HackershubNL/SmokeyMcSmokerson/Hardware/Smoker/Fan Mount Front.SLDPRT

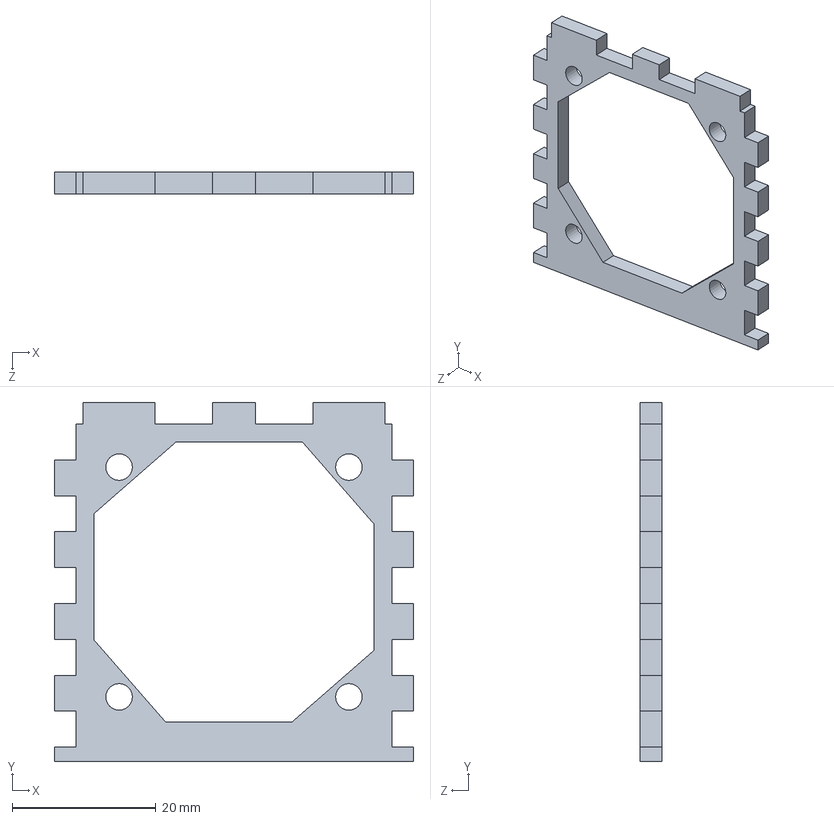
[picture p20: CAD file, 2019-05-26]
Hardware/Smoker/Fan Mount Front.SLDPRT
50.0 x 50.0 x 3.00 mm
