HackershubNL/SmokeyMcSmokerson/Hardware/Smoker/Inlet Spreader.SLDPRT

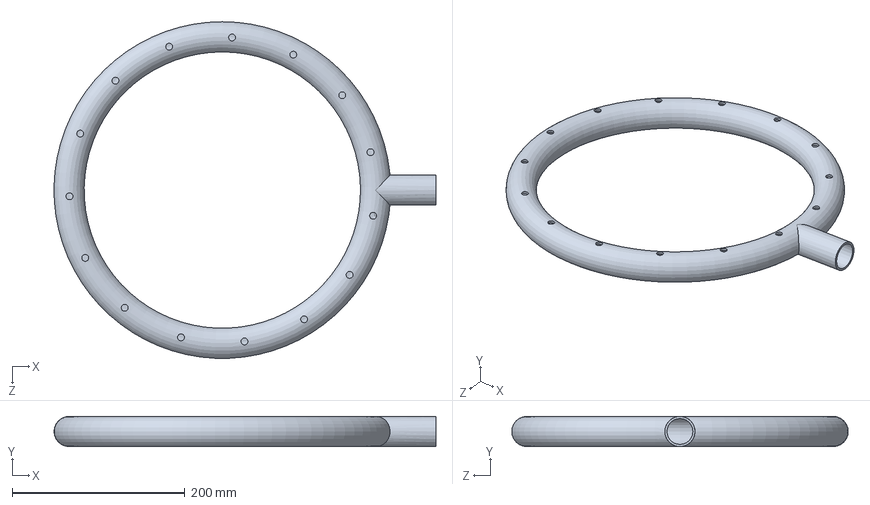
[picture p21: CAD file, 2019-05-26]
Hardware/Smoker/Inlet Spreader.SLDPRT
442.5 x 35.0 x 389.8 mm
