HackershubNL/SmokeyMcSmokerson/Hardware/Smoker/Controller Bracket V2.SLDPRT

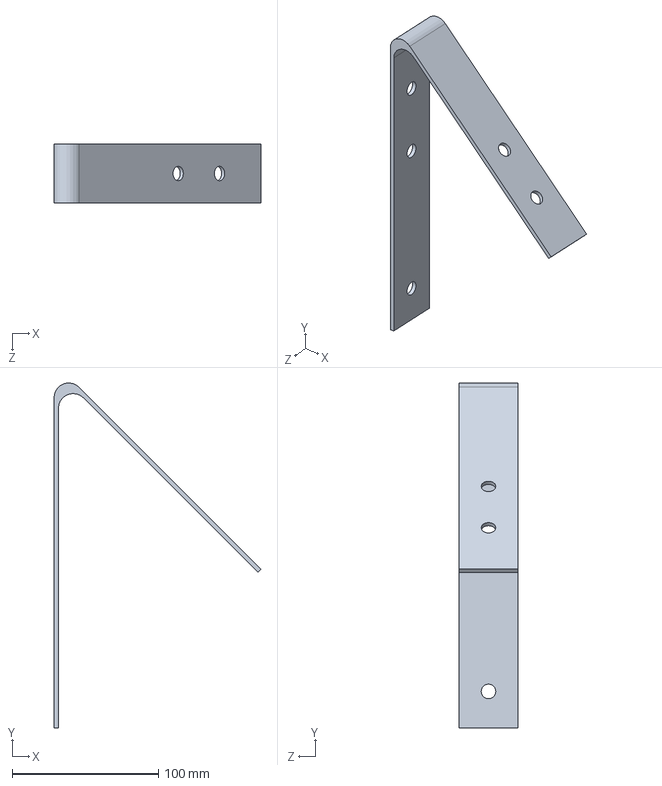
[picture p22: CAD file, 2019-05-26]
Hardware/Smoker/Controller Bracket V2.SLDPRT
141.4 x 235.8 x 40.0 mm
