HackershubNL/SmokeyMcSmokerson/Hardware/Smoker/Barrel.SLDPRT

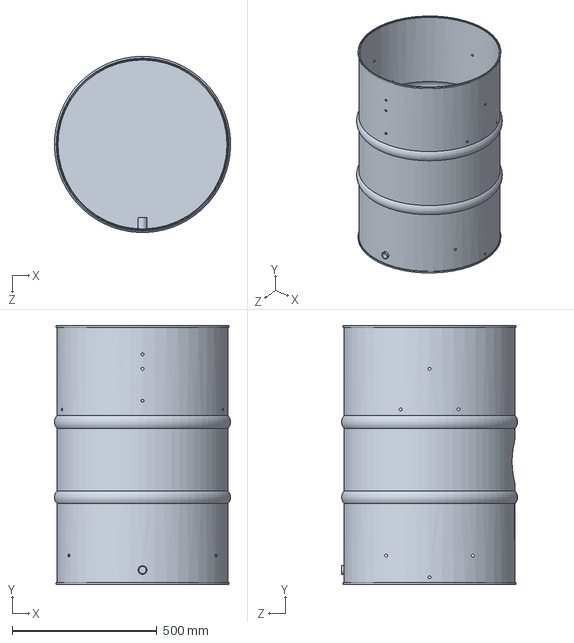
[picture p23: CAD file, 2019-05-26]
Hardware/Smoker/Barrel.SLDPRT
608.8 x 895.1 x 609.3 mm
