HackershubNL/SmokeyMcSmokerson/Hardware/Smoker/Header 2_54 Vertical 1x4.SLDPRT

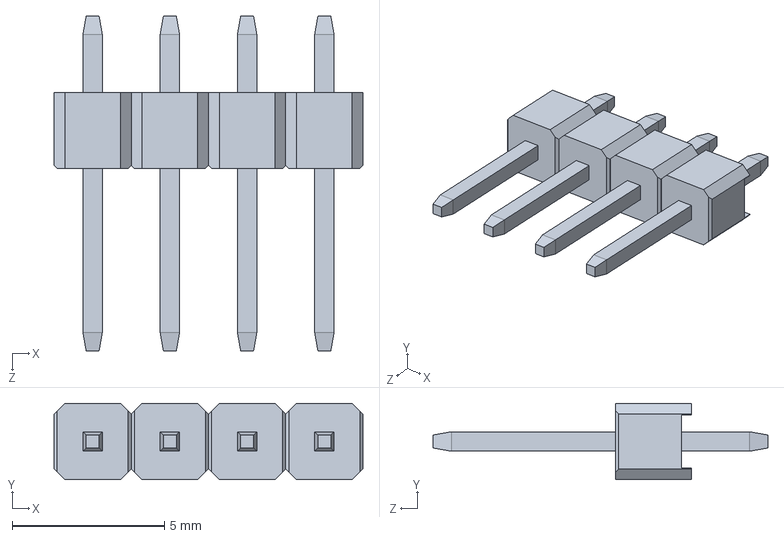
[picture p24: CAD file, 2019-05-26]
Hardware/Smoker/Header 2_54 Vertical 1x4.SLDPRT
10.2 x 2.50 x 11.0 mm
