HackershubNL/SmokeyMcSmokerson/Hardware/Smoker/Grill.SLDPRT

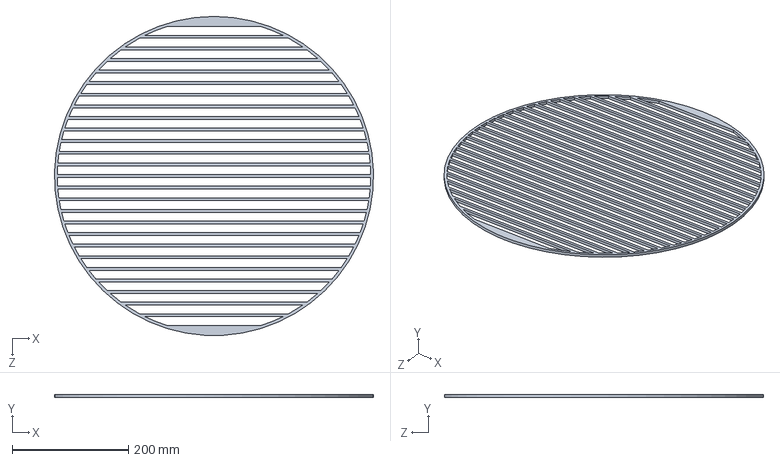
[picture p25: CAD file, 2019-05-26]
Hardware/Smoker/Grill.SLDPRT
549.8 x 5.00 x 550.0 mm
