HackershubNL/SmokeyMcSmokerson/Hardware/Smoker/Fan Mount Base.SLDPRT

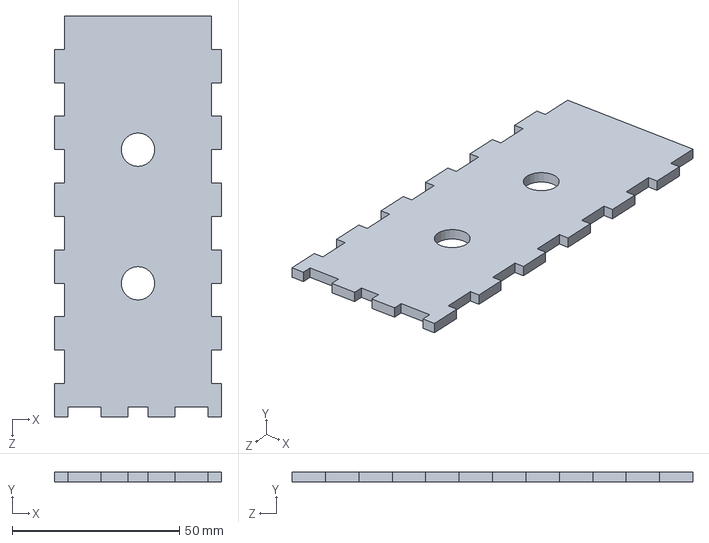
[picture p26: CAD file, 2019-05-26]
Hardware/Smoker/Fan Mount Base.SLDPRT
50.0 x 3.00 x 120.0 mm
