HackershubNL/SmokeyMcSmokerson/Hardware/Smoker/Led.SLDPRT

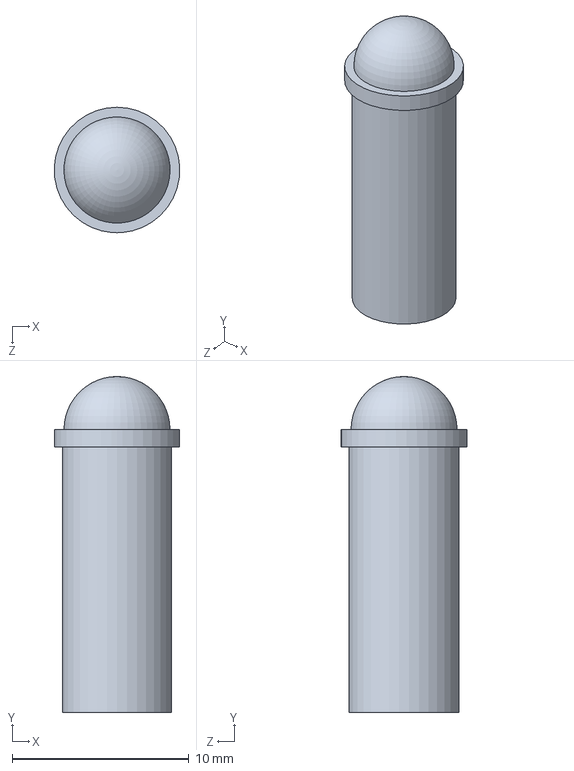
[picture p27: CAD file, 2019-05-26]
Hardware/Smoker/Led.SLDPRT
7.09 x 19.0 x 7.10 mm
