HackershubNL/SmokeyMcSmokerson/Hardware/Smoker/Controller Bracket.SLDPRT

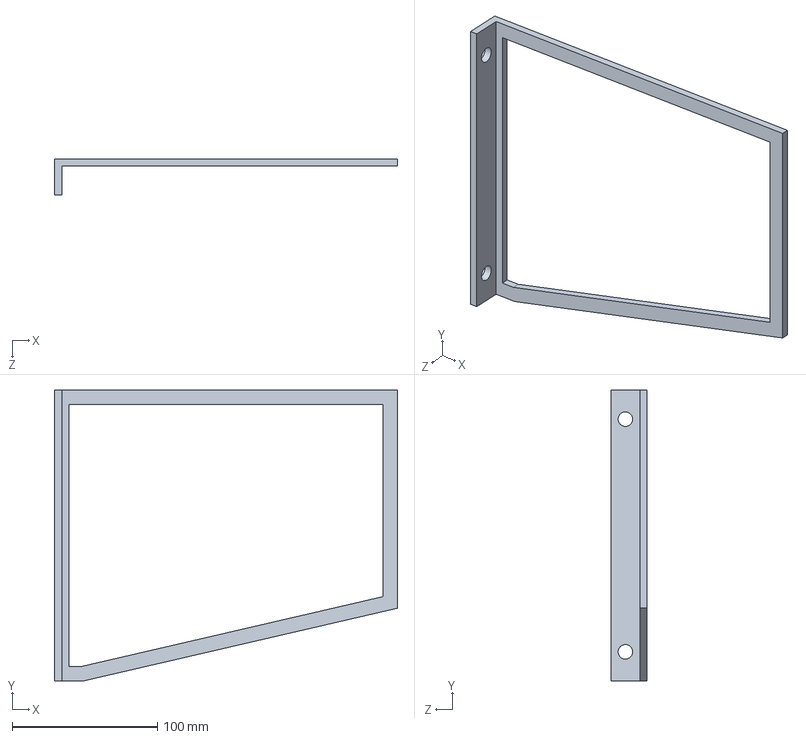
[picture p28: CAD file, 2019-05-26]
Hardware/Smoker/Controller Bracket.SLDPRT
235.9 x 200.0 x 25.0 mm
