HackershubNL/SmokeyMcSmokerson/Hardware/Smoker/Controller Box Base.SLDPRT

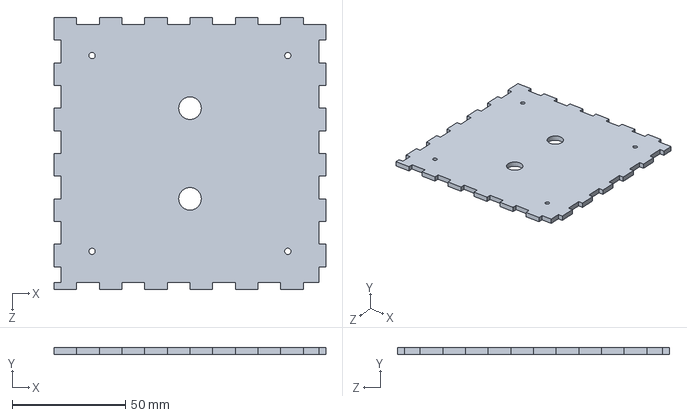
[picture p29: CAD file, 2019-05-26]
Hardware/Smoker/Controller Box Base.SLDPRT
120.0 x 3.00 x 120.0 mm
