HackershubNL/SmokeyMcSmokerson/Hardware/Smoker/GPIO Header.SLDPRT

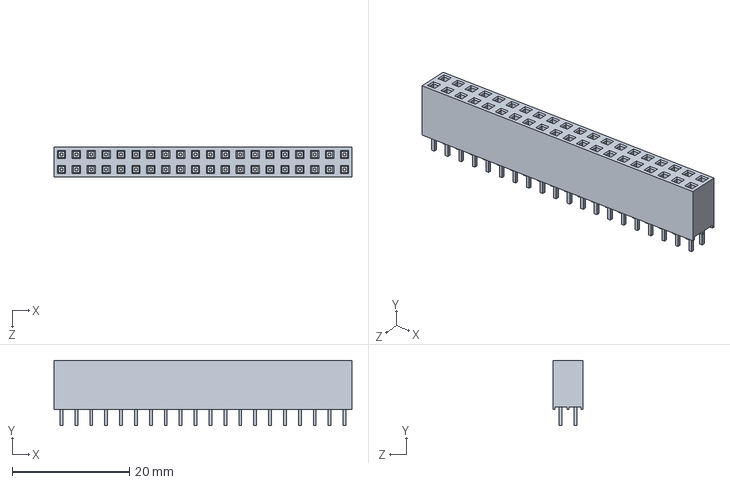
[picture p30: CAD file, 2019-05-26]
Hardware/Smoker/GPIO Header.SLDPRT
50.8 x 11.1 x 5.08 mm
