HackershubNL/SmokeyMcSmokerson/Hardware/Smoker/Water Pan.SLDPRT

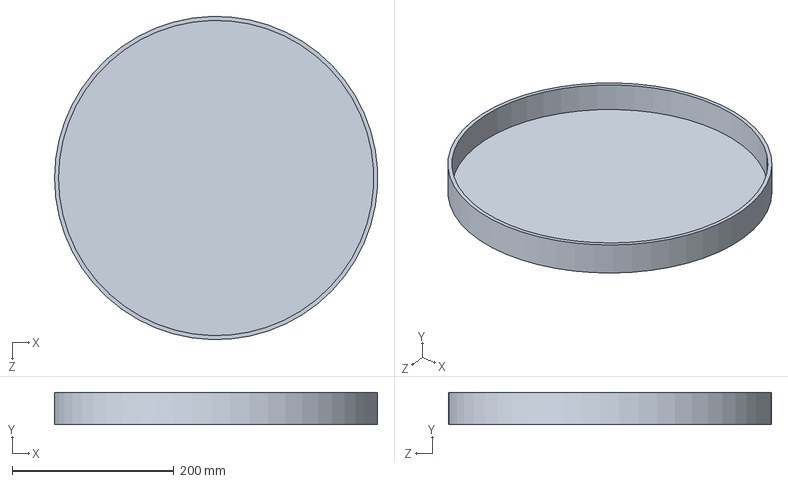
[picture p31: CAD file, 2019-05-26]
Hardware/Smoker/Water Pan.SLDPRT
399.6 x 40.0 x 399.8 mm
