HackershubNL/SmokeyMcSmokerson/Hardware/Smoker/Coal Shute.SLDPRT

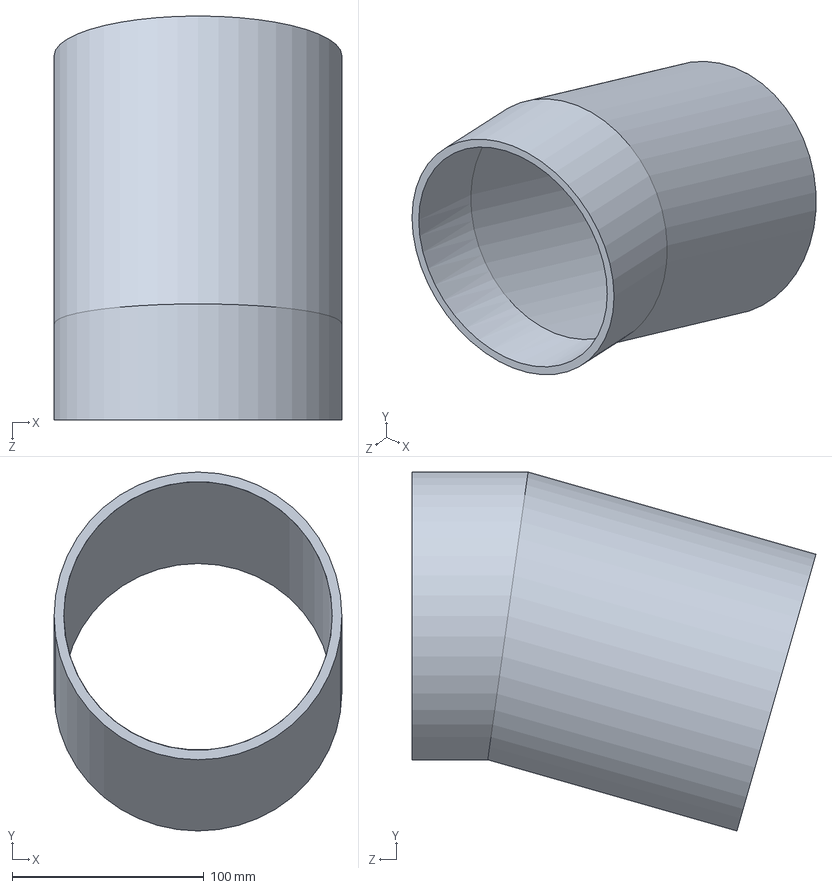
[picture p32: CAD file, 2019-05-26]
Hardware/Smoker/Coal Shute.SLDPRT
150.0 x 187.1 x 210.6 mm
