HackershubNL/SmokeyMcSmokerson/Hardware/Smoker/Place Holder Fan.SLDPRT

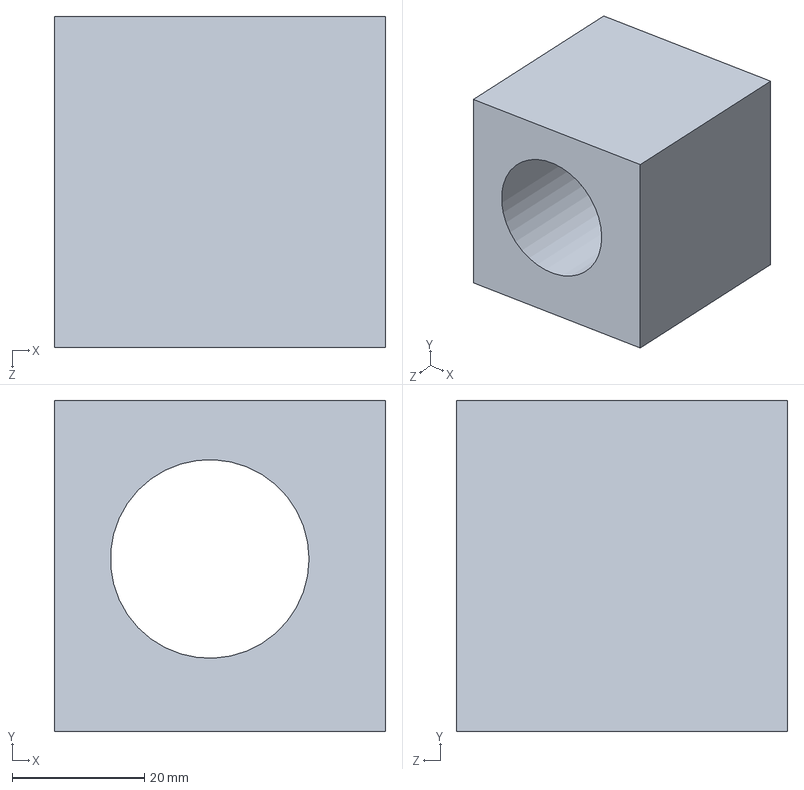
[picture p33: CAD file, 2019-05-26]
Hardware/Smoker/Place Holder Fan.SLDPRT
50.0 x 50.0 x 50.0 mm
