HackershubNL/SmokeyMcSmokerson/Hardware/Smoker/Cone Baffle.SLDPRT

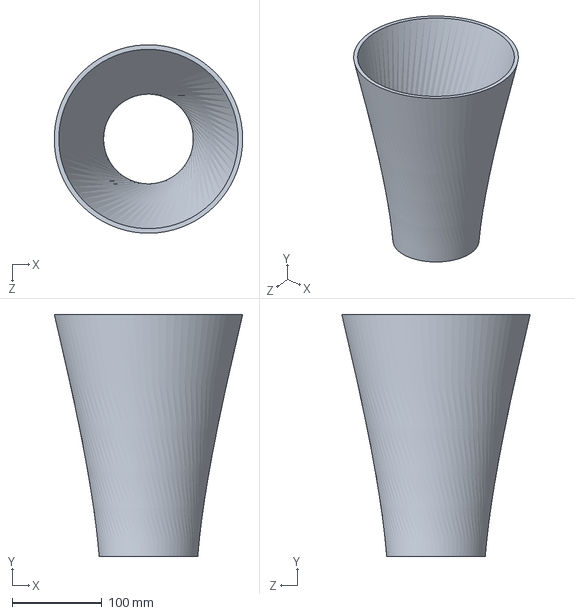
[picture p34: CAD file, 2019-05-26]
Hardware/Smoker/Cone Baffle.SLDPRT
210.2 x 270.0 x 210.3 mm
