HackershubNL/SmokeyMcSmokerson/Hardware/Smoker/Fan Mount Side.SLDPRT

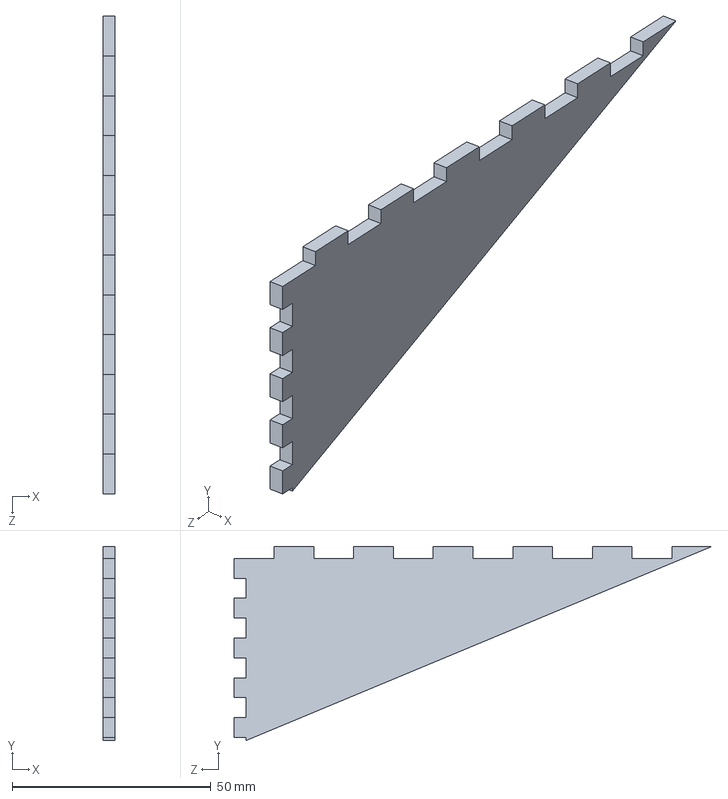
[picture p35: CAD file, 2019-05-26]
Hardware/Smoker/Fan Mount Side.SLDPRT
3.00 x 48.8 x 120.0 mm
