HackershubNL/SmokeyMcSmokerson/Hardware/Smoker/Rocker Switch.SLDPRT

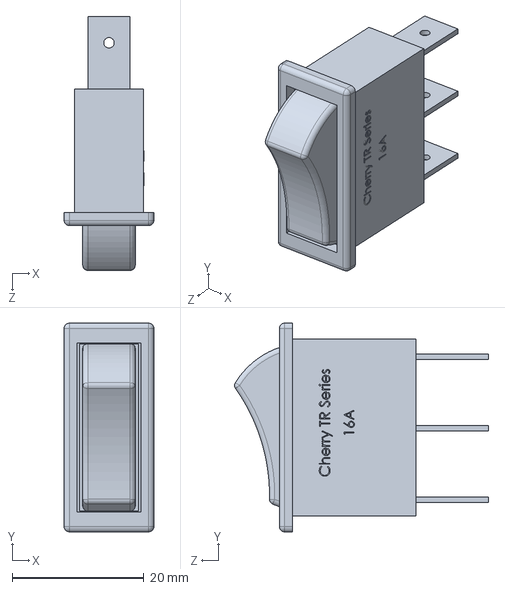
[picture p36: CAD file, 2019-05-26]
Hardware/Smoker/Rocker Switch.SLDPRT
13.7 x 31.8 x 38.6 mm
