HackershubNL/SmokeyMcSmokerson/Hardware/Smoker/LCD Screen.SLDPRT

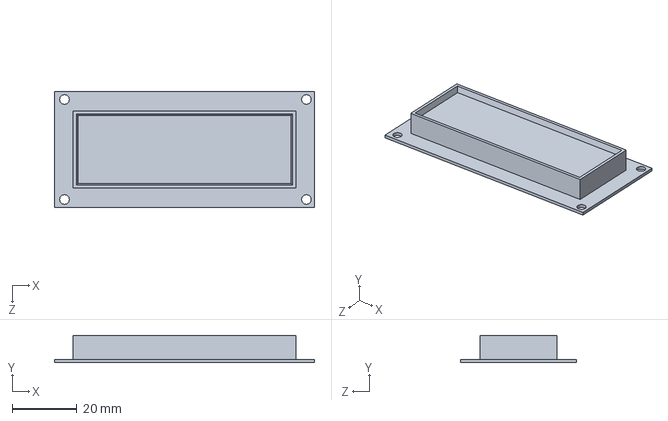
[picture p37: CAD file, 2019-05-26]
Hardware/Smoker/LCD Screen.SLDPRT
80.6 x 8.40 x 36.0 mm
