HackershubNL/SmokeyMcSmokerson/Hardware/Smoker/Dome Lid.SLDPRT

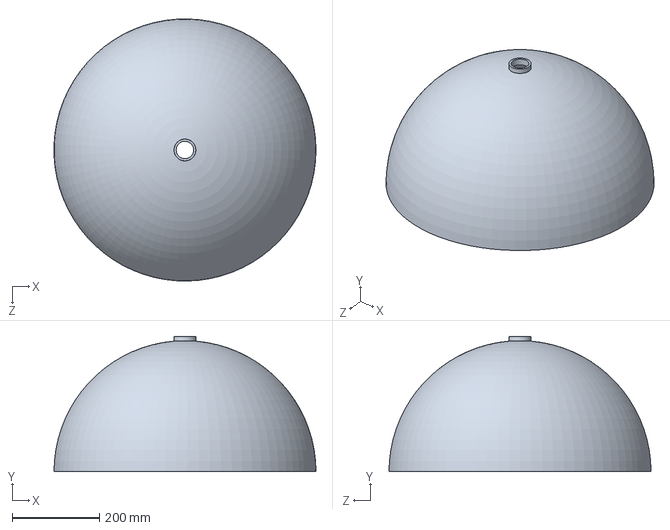
[picture p38: CAD file, 2019-05-26]
Hardware/Smoker/Dome Lid.SLDPRT
599.7 x 310.0 x 599.9 mm
