HackershubNL/SmokeyMcSmokerson/Hardware/Smoker/Coal Basket.SLDPRT

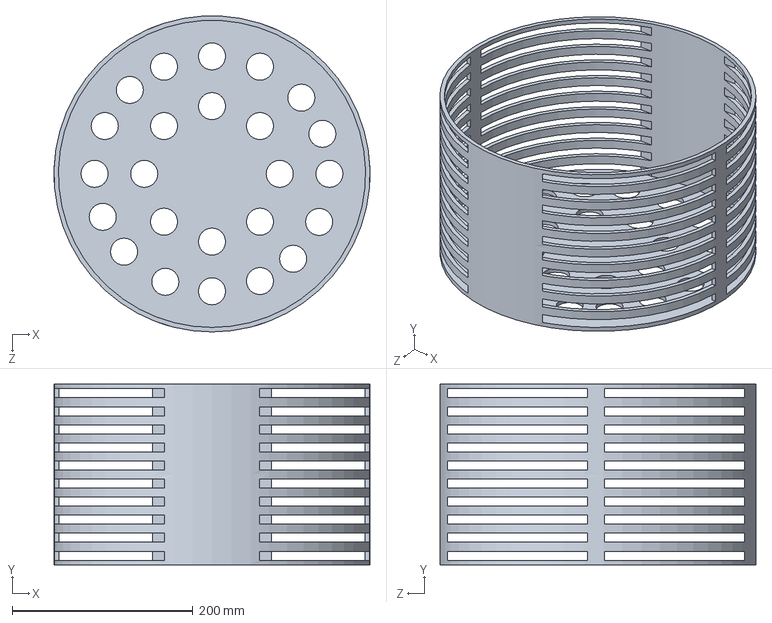
[picture p39: CAD file, 2019-05-26]
Hardware/Smoker/Coal Basket.SLDPRT
349.8 x 200.0 x 349.7 mm
