HackershubNL/SmokeyMcSmokerson/Hardware/Smoker/I2C Screen Module.SLDPRT

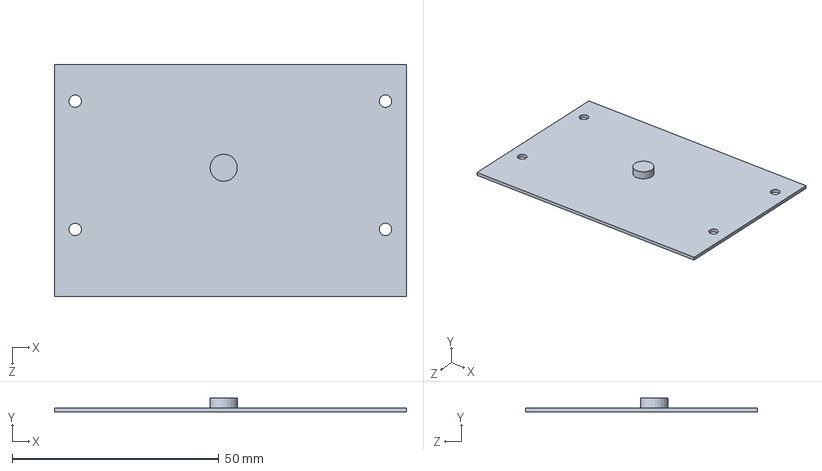
[picture p40: CAD file, 2019-05-26]
Hardware/Smoker/I2C Screen Module.SLDPRT
85.1 x 3.50 x 56.1 mm
