HackershubNL/SmokeyMcSmokerson/Hardware/Smoker/40mm Fan.SLDPRT

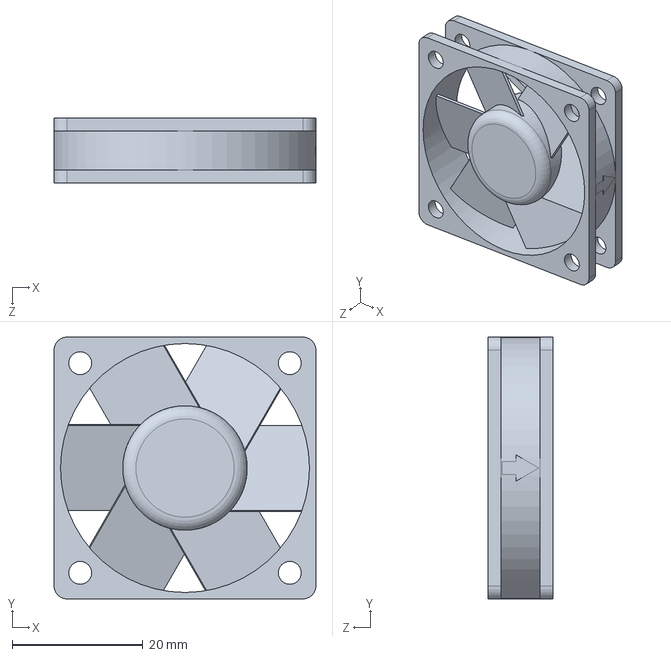
[picture p41: CAD file, 2019-05-26]
Hardware/Smoker/40mm Fan.SLDPRT
40.0 x 40.0 x 10.0 mm
